ppsilv/vgaTerminal/Insumos/z80-002.jpeg

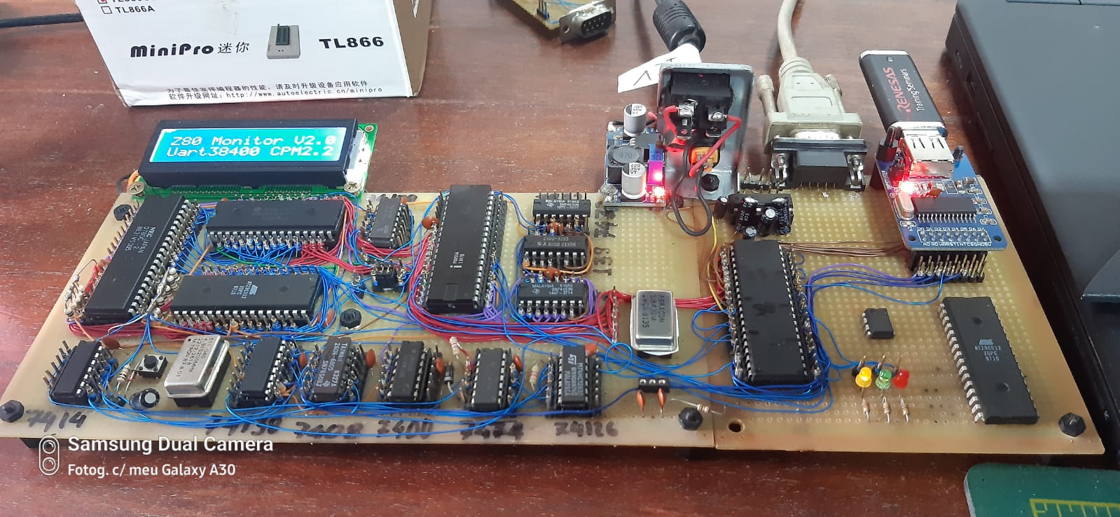
Insumos/z80-002.jpeg
