ppsilv/vgaTerminal/Insumos/z80-003.jpeg

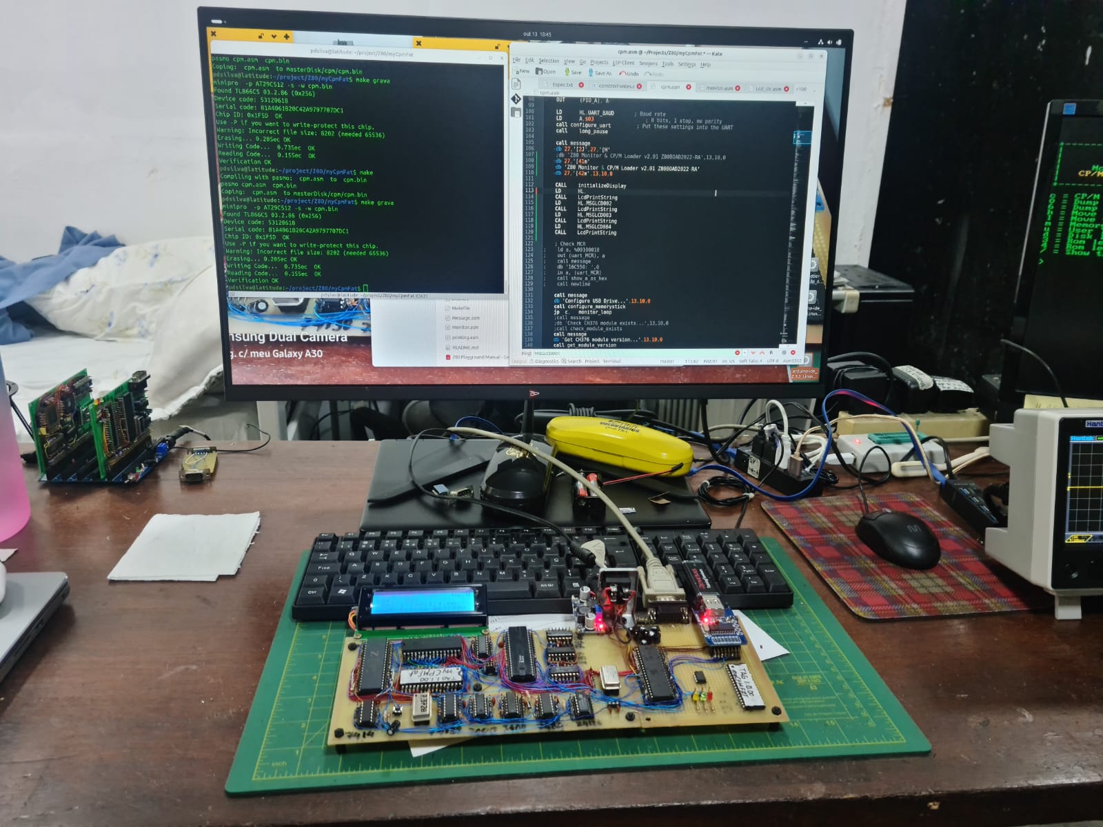
Insumos/z80-003.jpeg
