ppsilv/vgaTerminal/Docs/RS232_male2female.jpg

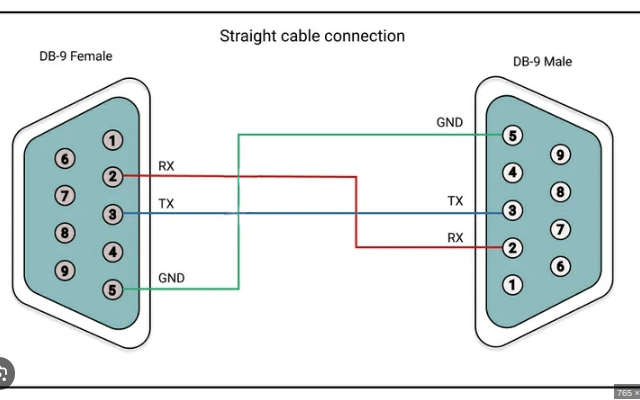
Docs/RS232_male2female.jpg
