ppsilv/vgaTerminal/Insumos/z80-001.jpeg

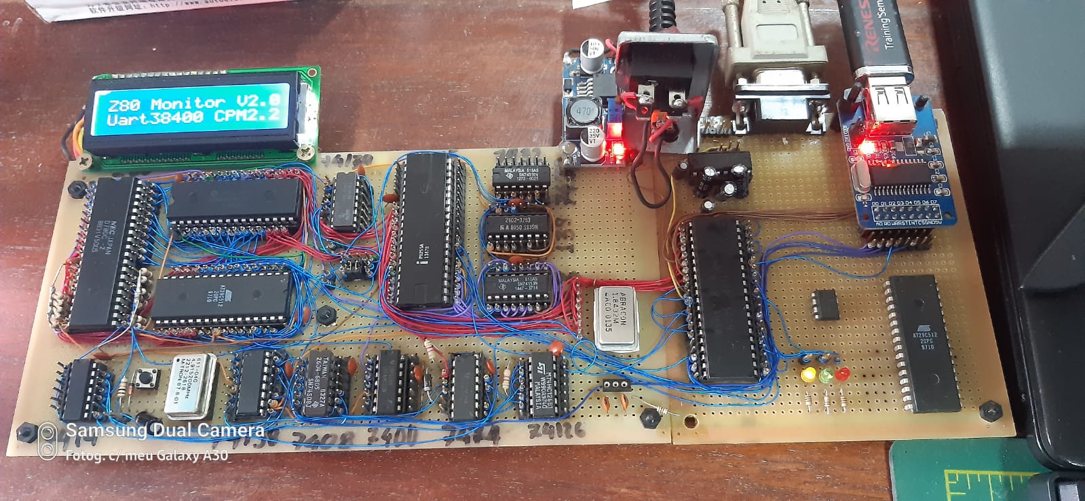
Insumos/z80-001.jpeg
