ppsilv/vgaTerminal/Insumos/z80-004.jpeg

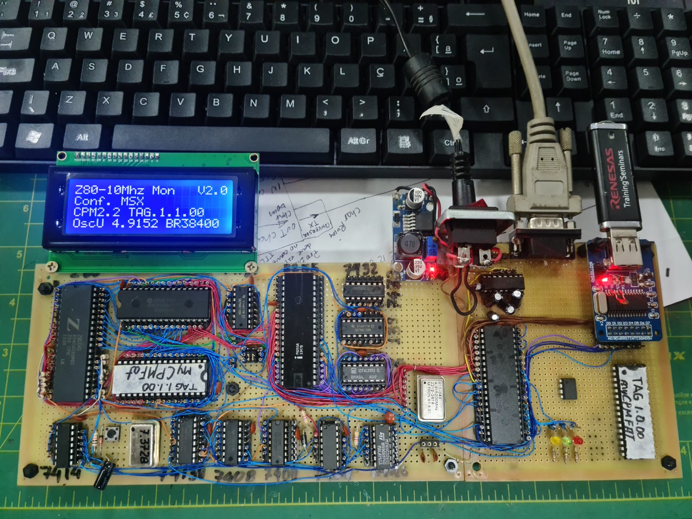
Insumos/z80-004.jpeg
