ppsilv/vgaTerminal/Insumos/z80-005.jpeg

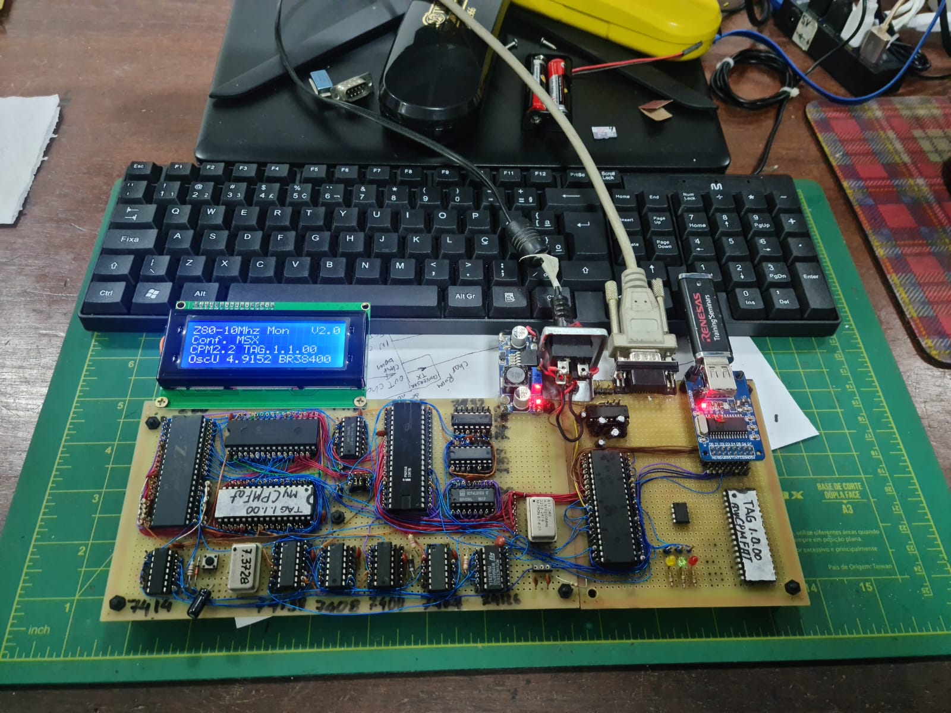
Insumos/z80-005.jpeg
