ppsilv/vgaTerminal/schematic/AnsiTerminal/AnsiTerminal.kicad_sch

## KiCad design schematic/AnsiTerminal/AnsiTerminal.kicad_sch (2024-10-10, an earlier design)

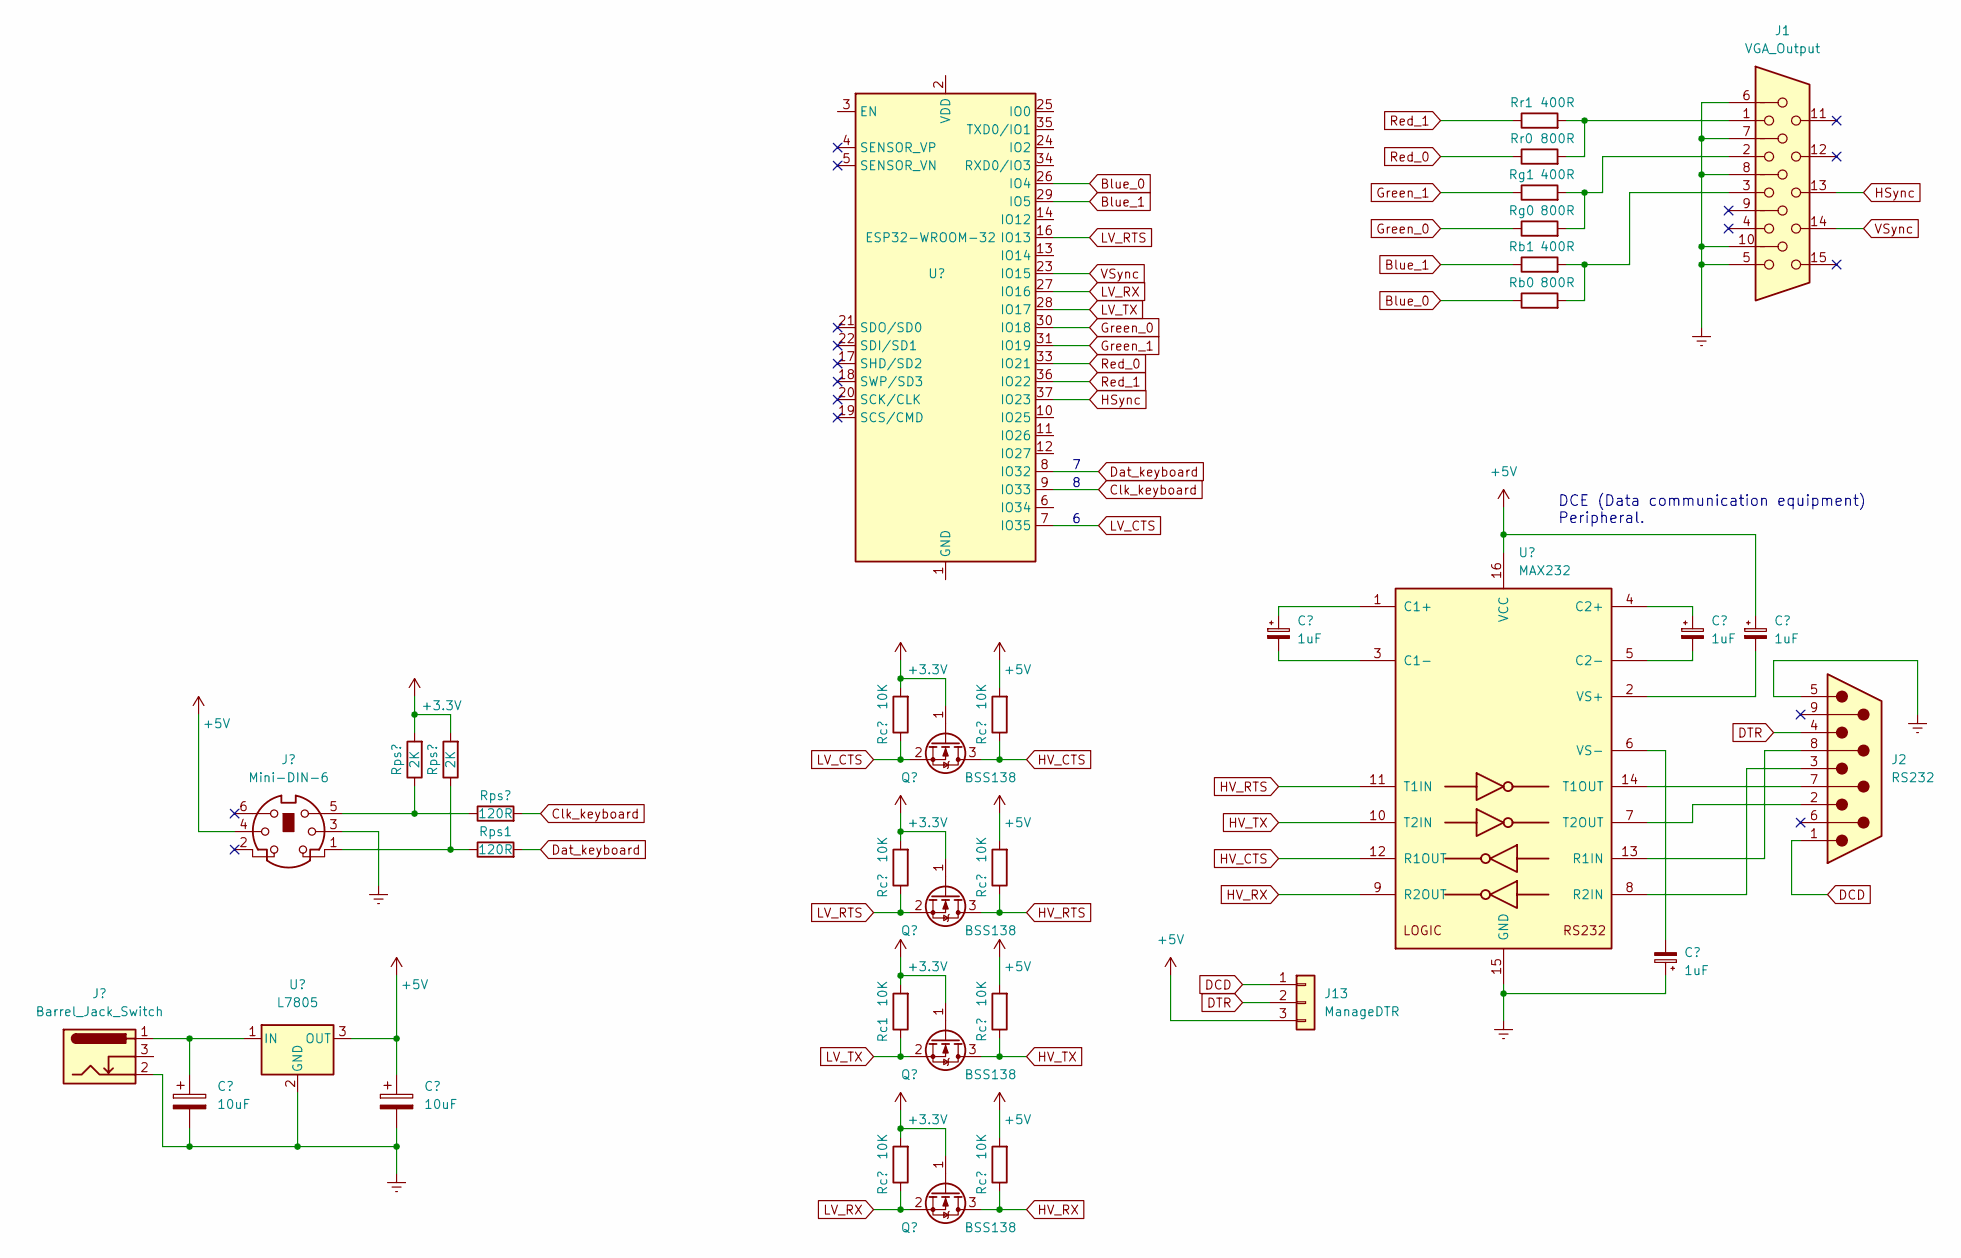
[picture p18: schematic AnsiTerminal.kicad_sch]

Parts:
J1: VGA_Output
J2: RS232
J13: ManageDTR
Rb0: 800R
Rb1: 400R
Rc1: 10K
Rg0: 800R
Rg1: 400R
Rps1: 120R
Rr0: 800R
Rr1: 400R

Connections:
Blue_0: Rb0.1
Blue_1: Rb1.1
DCD: J2.1, J13.1
DTR: J2.4, J13.2
Dat_keyboard: Rps1.2
Green_0: Rg0.1
Green_1: Rg1.1
HSync: J1.13
LV_TX: Rc1.1
unnamed: J1.1, Rr0.2, Rr1.2
unnamed: J1.2, Rg0.2, Rg1.2
unnamed: J1.3, Rb0.2, Rb1.2
unnamed: J1.5, J1.6, J1.7, J1.8, J1.10
Red_0: Rr0.1
Red_1: Rr1.1
VSync: J1.14

Notes on the sheet:
DCE (Data communication equipment) Peripheral.
