ppsilv/vgaTerminal/ESP32Lib/src/Graphics/Graphics.h

/*
	Author: bitluni 2019, refactoring by Martin-Laclaustra 2020
	License: 
	Creative Commons Attribution ShareAlike 4.0
	https://creativecommons.org/licenses/by-sa/4.0/
	
	For further details check out: 
		https://youtube.com/bitlunislab
		https://github.com/bitluni
		http://bitluni.net
*/

/*
Virtual function still needed in child classes
Color** allocateFrameBuffer()
Most virtual functions have been moved to templated static inheritance:

Inherited from InterfaceColor
typedef TYPE Color
colormask()
Color RGBA(int r, int g, int b, int a = 255) const
int R(Color c) const
int G(Color c) const
int B(Color c) const
int A(Color c) const

These functions are wrapped in virtual methods
void _dotFast(int x, int y, Color color)
Color _getFast(int x, int y)

They are composed of smaller components:

Inherited from BufferLayout
typedef TYPE BufferUnit
xpixperunit
ypixperunit
bufferdatamask
replicate (unused)
replicate32
swx
swy
shval
shbuf

Inherited from ColorToBuffer
coltobuf
buftocol
*/

#pragma once
#include <stdlib.h>
#include <math.h>
#include "Font.h"
#include "ImageDrawer.h"

#include "InterfaceColors.h"
#include "BufferLayouts.h"
#include "ColorToBuffer.h"

// Color defines the interface color, all interactions should use this
// BufferUnit defines how the color is actually stored in memory
template<class InterfaceColor, class BufferLayout, class ColorToBuffer>
class Graphics: public ImageDrawer, public InterfaceColor, public BufferLayout, public ColorToBuffer
{
  public:
	typedef typename InterfaceColor::Color Color;
	typedef typename BufferLayout::BufferUnit BufferGraphicsUnit;
	int cursorX, cursorY, cursorBaseX, cursorXIncrement, cursorYIncrement;
	Color frontColor, backColor;
	Font *font;
	int frameBufferCount;
	int currentFrameBuffer;
	BufferGraphicsUnit **frameBuffers[3];
	BufferGraphicsUnit **frontBuffer;
	BufferGraphicsUnit **backBuffer;
	bool autoScroll;
	//bool onScroll;
	size_t sizeOfBufferUnit = sizeof(BufferGraphicsUnit);
	int storageCoefficient = 1; //number of pixels in an BufferUnit variable
	int defaultBufferValue = 0;

	int xres;
	int yres;

	//pass templated functions
	static const int graphics_colormask()
	{
		return InterfaceColor::static_colormask();
	}
	static int graphics_swx(int x)
	{
		return BufferLayout::static_swx(x);
	}
	static int graphics_swy(int y)
	{
		return BufferLayout::static_swy(y);
	}
	static int graphics_shval(BufferGraphicsUnit val, int x, int y)
	{
		return BufferLayout::static_shval(val, x, y);
	}
	static int graphics_shbuf(BufferGraphicsUnit val, int x, int y)
	{
		return BufferLayout::static_shbuf(val, x, y);
	}
	static int graphics_coltobuf(int val, int x, int y)
	{
		return ColorToBuffer::coltobuf(val, x, y);
	}
	static int graphics_buftocol(int val)
	{
		return ColorToBuffer::buftocol(val);
	}

	void _dotFast(int x, int y, Color color)
	{
		//basic concept
		//backBuffer[y][x] = color;
		//decide x or y position[sw] -> shift depending (or not) on x or y[shval] -> mask[colormask] -> erase bits
		backBuffer[BufferLayout::static_swy(y)][BufferLayout::static_swx(x)] &= ~BufferLayout::static_shval(BufferLayout::static_bufferdatamask() & InterfaceColor::static_colormask(), x, y); // delete bits
		//mask[colormask] -> convert to buffer[coltobuf] -> shift depending (or not) on x or y[shval] -> decide x or y position[sw] -> store data
		backBuffer[BufferLayout::static_swy(y)][BufferLayout::static_swx(x)] |= BufferLayout::static_shval(ColorToBuffer::coltobuf(color & InterfaceColor::static_colormask(), x, y) & BufferLayout::static_bufferdatamask(), x, y); // write new bits
	}
	virtual void dotFast(int x, int y, Color color)
	{
		_dotFast(x, y, color);
	}
	virtual void dot(int x, int y, Color color)
	{
		if ((unsigned int)x < xres && (unsigned int)y < yres)
			_dotFast(x, y, color);
	}
	virtual void dotAdd(int x, int y, Color color)
	{
		Color oldColor = get(x, y);
		Color newColor = colorAdd(oldColor, color);
		dot(x, y, newColor);
	}
	virtual void dotMix(int x, int y, Color color)
	{
		Color oldColor = get(x, y);
		Color newColor = colorMix(oldColor, color);
		dot(x, y, newColor);
	}
	Color _getFast(int x, int y)
	{
		//basic concept
		//return backBuffer[y][x];
		//decide x or y position[sw] -> retrieve data -> shift depending (or not) on x or y[shbuf] -> mask[colormask] -> convert to color[buftocol]
		return ColorToBuffer::buftocol(BufferLayout::static_shbuf(backBuffer[BufferLayout::static_swy(y)][BufferLayout::static_swx(x)], x, y) & InterfaceColor::static_colormask());
	}
	virtual Color getFast(int x, int y)
	{
		return _getFast(x, y);
	}
	virtual Color get(int x, int y)
	{
		if ((unsigned int)x < xres && (unsigned int)y < yres)
			return _getFast(x, y);
		return 0;
	}
	//virtual BufferGraphicsUnit** allocateFrameBuffer() = 0;
	virtual BufferGraphicsUnit** allocateFrameBuffer()
	{
		//GraphicsCA8Swapped
		//return Graphics::allocateFrameBuffer(xres, yres, (BufferGraphicsUnit)levelBlack);
		//GraphicsR5G5B4S2Swapped
		//return Graphics::allocateFrameBuffer(xres, yres, (BufferGraphicsUnit)SBits);
		//GraphicsX8CA8Swapped
		//return Graphics::allocateFrameBuffer(xres, yres, (BufferGraphicsUnit)levelBlack<<8);
		//GraphicsX6S2W8RangedSwapped
		//return Graphics::allocateFrameBuffer(xres, yres, (BufferGraphicsUnit)(colorMinValue<<8)|SBits);
		//GraphicsW8RangedSwapped
		//return Graphics::allocateFrameBuffer(xres, yres, (BufferGraphicsUnit)colorMinValue);
		//GraphicsTextBuffer
		//return Graphics::allocateFrameBuffer(xres, yres, (BufferGraphicsUnit)32);
		//GraphicsW8
		//return Graphics::allocateFrameBuffer(xres, yres, (BufferGraphicsUnit)0);
		//GraphicsW1
		//return Graphics::allocateFrameBuffer(4*((xres + 3) / 4), (yres + static_ypixperunit() - 1) / static_ypixperunit(), (BufferGraphicsUnit)0);
		//GraphicsR5G5B4A2
		//return Graphics::allocateFrameBuffer(xres, yres, (BufferGraphicsUnit)0);
		//GraphicsR2G2B2S2Swapped
		//return Graphics::allocateFrameBuffer(xres, yres, (BufferGraphicsUnit)SBits);
		//GraphicsR2G2B2A2
		//return Graphics::allocateFrameBuffer(xres, yres, (BufferGraphicsUnit)0);
		//GraphicsR1G1B1X3S2Swapped
		//return Graphics::allocateFrameBuffer(xres, yres, (BufferGraphicsUnit)SBits);
		//GraphicsR1G1B1A1
		//return Graphics::allocateFrameBuffer((xres + static_xpixperunit() - 1) / static_xpixperunit(), yres, (BufferGraphicsUnit)0);
		return Graphics::allocateFrameBuffer(
			(xres + BufferLayout::static_xpixperunit() - 1) / BufferLayout::static_xpixperunit(),
			(yres + BufferLayout::static_ypixperunit() - 1) / BufferLayout::static_ypixperunit(),
			(BufferGraphicsUnit)defaultBufferValue);
		//TODO Fixes:
		// - round up x to multiples of 4 bytes (when necessary: in GraphicsW1 for renderer, in DMA buffers)
		//TODO:
		// - calculate and use byte-based allocation instead of unit/pixel based allocation
		//   (at this stage for some buffers the size of the buffer =/= xres, so in the next function "xres" is not such any more)
		// - move elsewhere: acondition the buffer with the fixed sync bytes or blank values
		//   this has to be done for all buffers allocated (front, back, and reserve)
	}
	virtual BufferGraphicsUnit** allocateFrameBuffer(int xres, int yres, BufferGraphicsUnit value)
	{
		BufferGraphicsUnit** frame = (BufferGraphicsUnit **)malloc(yres * sizeof(BufferGraphicsUnit *) );
		if(!frame)
			ERROR("Not enough memory for frame buffer");
		for (int y = 0; y < yres; y++)
		{
			frame[y] = (BufferGraphicsUnit *)malloc(xres * sizeof(BufferGraphicsUnit)+1000);
			if(!frame[y])
				ERROR("Not enough memory for frame buffer");
			for (int x = 0; x < xres; x++)
				frame[y][x] = value;
		}
		return frame;
	}
	static void **allocateRegularBufferArray(int count, int bytes)
	{
		void **arr = (void **)malloc(count * sizeof(void *));
		if(!arr)
			ERROR("Not enough regular memory");
		for (int i = 0; i < count; i++)
		{
			arr[i] = (void *)malloc(bytes);
			if(!arr[i])
				ERROR("Not enough regular memory");
		}
		return arr;
	}
	virtual Color colorAdd(Color colorOld, Color colorNew)
	{
		return InterfaceColor::static_colorAdd(colorOld, colorNew);
	}
	// Generic function currently not in use
	//virtual Color colorAdd(Color colorOld, Color colorNew)
	//{
		//int newR = R(colorOld)+R(colorNew);
		//newR = (newR > 255) ? 255 : newR;
		//int newG = G(colorOld)+G(colorNew);
		//newG = (newG > 255) ? 255 : newG;
		//int newB = B(colorOld)+B(colorNew);
		//newB = (newB > 255) ? 255 : newB;
		//int newA = A(colorOld)+A(colorNew);
		//newA = (newA > 255) ? 255 : newA;
		//return RGBA(newR, newG, newB, newA);
	//}
	virtual Color colorMix(Color colorOld, Color colorNew)
	{
		return InterfaceColor::static_colorMix(colorOld, colorNew);
	}
	// Generic function currently not in use
	//virtual Color colorMix(Color colorOld, Color colorNew)
	//{
		//int colorNewA = A(colorNew);
		//if (colorNewA != 0)
		//{
			//colorNewA = colorNewA + 1;
			//int newR = (R(colorOld)*(256-colorNewA)+R(colorNew)*colorNewA)>>8;
			//int newG = (G(colorOld)*(256-colorNewA)+G(colorNew)*colorNewA)>>8;
			//int newB = (B(colorOld)*(256-colorNewA)+B(colorNew)*colorNewA)>>8;
			//return RGBA(newR, newG, newB);
		//} else {
			//return colorOld;
		//}
	//}
	virtual Color RGBA(int r, int g, int b, int a = 255) const
	{
		return InterfaceColor::static_RGBA(r, g, b, a);
	}
	virtual int R(Color c) const
	{
		return InterfaceColor::static_R(c);
	}
	virtual int G(Color c) const
	{
		return InterfaceColor::static_G(c);
	}
	virtual int B(Color c) const
	{
		return InterfaceColor::static_B(c);
	}
	virtual int A(Color c) const
	{
		return InterfaceColor::static_A(c);
	}
	Color RGB(unsigned long rgb) const 
	{
		return RGBA(rgb & 255, (rgb >> 8) & 255, (rgb >> 16) & 255);
	}
	Color RGBA(unsigned long rgba) const 
	{
		return RGBA(rgba & 255, (rgba >> 8) & 255, (rgba >> 16) & 255, rgba >> 24);
	}
	Color RGB(int r, int g, int b) const 
	{
		return RGBA(r, g, b);
	}

	void setFrameBufferCount(unsigned char i)
	{
		frameBufferCount = i > 3 ? 3 : i;
	}

	virtual void show(bool vSync = false)
	{
		if(!frameBufferCount)
			return;
		currentFrameBuffer = (currentFrameBuffer + 1) % frameBufferCount;
		frontBuffer = frameBuffers[currentFrameBuffer];
		backBuffer = frameBuffers[(currentFrameBuffer + frameBufferCount - 1) % frameBufferCount];
		Serial.print("yres * sizeof(BufferGraphicsUnit *).:");
		Serial.println(yres * sizeof(BufferGraphicsUnit *));
		//Serial.print("frameBufferCount...:");Serial.println(frameBufferCount);
		//Serial.print("backBuffer.........:");Serial.println(backBuffer);
	}

	Graphics(int xres = 0, int yres = 0)
	{
		this->xres = xres;
		this->yres = yres;
		font = 0;
		cursorX = cursorY = cursorBaseX = 0;
		cursorXIncrement = cursorYIncrement = 1;
		frontColor = -1;
		backColor = 0;
		frameBufferCount = 1;
		for(int i = 0; i < 3; i++)
			frameBuffers[i] = 0;
		frontBuffer = 0;
		backBuffer = 0;
		autoScroll = true;
	}

	virtual bool allocateFrameBuffers()
	{
		if(yres <= 0 || xres <= 0)
			return false;
		for(int i = 0; i < frameBufferCount; i++)
			frameBuffers[i] = allocateFrameBuffer();
		currentFrameBuffer = 0;
		show();
		return true;
	}

	virtual void setResolution(int xres, int yres)
	{
		this->xres = xres;
		this->yres = yres;
		allocateFrameBuffers();
	}

	virtual float pixelAspect() const
	{
		return 1;
	}

	void setTextColor(long front, long back = 0)
	{
		frontColor = front;
		backColor = back;
	}

	virtual void setFont(Font &font)
	{
		this->font = &font;
		cursorXIncrement = this->font->charWidth;
		cursorYIncrement = this->font->charHeight;
	}

	void setCursor(int x, int y)
	{
		cursorX = cursorBaseX = x;
		cursorY = y;
	}

	void setCursorText(int x, int y)
	{
		cursorX = cursorBaseX = x * font->charWidth;
		cursorY = y * font->charHeight;
	}


	virtual void drawChar(int x, int y, int ch)
	{
		if (!font)
			return;
		if (!font->valid(ch))
			return;
		const unsigned char *pix = &font->pixels[font->charWidth * font->charHeight * (ch - font->firstChar)];
		for (int py = 0; py < font->charHeight; py++)
			for (int px = 0; px < font->charWidth; px++)
				if (*(pix++))
					dotMix(px + x, py + y, frontColor);
				else
					dotMix(px + x, py + y, backColor);
	}

	virtual void drawChar(int ch,bool clear)
	{
		if( clear ){
			for (int py = 0; py < font->charHeight; py++)
				for (int px = 0; px < font->charWidth; px++)
					dot(px + cursorX, py + cursorY, backColor);
		}else{
			const unsigned char *pix = &font->pixels[font->charWidth * font->charHeight * (ch - font->firstChar)];
			for (int py = 0; py < font->charHeight; py++)
				for (int px = 0; px < font->charWidth; px++)
					if (*(pix++))
						dot(px + cursorX, py + cursorY, frontColor);
					else
						dot(px + cursorX, py + cursorY, backColor);
		}
	}
	void printCursor(void)
	{
		drawChar('_',false);
	}

	void clearCursor(void)
	{
		drawChar('_',true);
	}

	void setCursorBS()
	{
		//Serial.println(cursorX);
		if (cursorX == 0){
			cursorY -= this->font->charHeight;
			cursorX = 79*this->font->charWidth;
		}else{
			cursorX -= this->font->charWidth;
		}
		//cursorY += y;
	}

	void print(const char ch)
	{
		if (!font)
			return;

		if(ch == '\n')
		{
			cursorX = 0;//cursorBaseX;
			cursorY += cursorYIncrement;
		}
		else if (font->valid(ch)){
			drawChar(cursorX, cursorY, ch);
			cursorX += cursorXIncrement;
		}
		else{
			drawChar(cursorX, cursorY, ' ');
		}

		if ( (cursorX + cursorXIncrement) > xres )
		{
			cursorY += cursorYIncrement;
			cursorX = cursorBaseX;
			if( cursorY > yres ){
				cursorY = yres-cursorYIncrement;
			}
		}
		if ( (cursorY + cursorYIncrement) > yres  )
		{
			if(autoScroll && ( (cursorY + cursorYIncrement) > yres) ){
				//onScroll = true;
				//Serial.print("\nCursorY ");Serial.print(cursorY);
				//Serial.print(" yres ");Serial.print(yres);
				//Serial.print(" cursorYIncrement ");Serial.print(cursorYIncrement);
				scroll((cursorY - yres)+cursorYIncrement, backColor);
			}
		}
	}
	//bool getOnScroll(){
	//	return onScroll;
	//}
	void println(const char ch)
	{
		print(ch);
		print("\n");
	}

	void print(const char *str)
	{
		if (!font)
			return;
		while (*str)
		{
			print(*str);
			str++;
		}
	}

	void println(const char *str)
	{
		print(str);
		print("\n");
	}

	void print(long number, int base = 10, int minCharacters = 1)
	{
		if(minCharacters < 1)
			minCharacters = 1;
		bool sign = number < 0;
		if (sign)
			number = -number;
		const char baseChars[] = "0123456789ABCDEF";
		char temp[33];
		temp[32] = 0;
		int i = 31;
		do
		{
			temp[i--] = baseChars[number % base];
			number /= base;
		} while (number > 0);
		if (sign)
			temp[i--] = '-';
		for (; i > 31 - minCharacters; i--)
			temp[i] = ' ';
		print(&temp[i + 1]);
	}

	void print(unsigned long number, int base = 10, int minCharacters = 1)
	{
		if(minCharacters < 1)
			minCharacters = 1;
		const char baseChars[] = "0123456789ABCDEF";
		char temp[33];
		temp[32] = 0;
		int i = 31;
		do
		{
			temp[i--] = baseChars[number % base];
			number /= base;
		} while (number > 0);
		for (; i > 31 - minCharacters; i--)
			temp[i] = ' ';
		print(&temp[i + 1]);
	}	

	void println(long number, int base = 10, int minCharacters = 1)
	{
		print(number, base, minCharacters); print("\n");
	}

	void println(unsigned long number, int base = 10, int minCharacters = 1)
	{
		print(number, base, minCharacters); print("\n");
	}

	void print(int number, int base = 10, int minCharacters = 1)
	{
		print(long(number), base, minCharacters);
	}

	void println(int number, int base = 10, int minCharacters = 1)
	{
		println(long(number), base, minCharacters);
	}

	void print(unsigned int number, int base = 10, int minCharacters = 1)
	{
		print((unsigned long)(number), base, minCharacters);
	}

	void println(unsigned int number, int base = 10, int minCharacters = 1)
	{
		println((unsigned long)(number), base, minCharacters);
	}

	void print(short number, int base = 10, int minCharacters = 1)
	{
		print(long(number), base, minCharacters);
	}

	void println(short number, int base = 10, int minCharacters = 1)
	{
		println(long(number), base, minCharacters);
	}

	void print(unsigned short number, int base = 10, int minCharacters = 1)
	{
		print(long(number), base, minCharacters);
	}

	void println(unsigned short number, int base = 10, int minCharacters = 1)
	{
		println(long(number), base, minCharacters);
	}

	void print(unsigned char number, int base = 10, int minCharacters = 1)
	{
		print(long(number), base, minCharacters);
	}

	void println(unsigned char number, int base = 10, int minCharacters = 1)
	{
		println(long(number), base, minCharacters);
	}

	void println()
	{
		print("\n");
	}

	void print(double number, int fractionalDigits = 2, int minCharacters = 1)
	{
		long p = long(pow(10, fractionalDigits));
		long long n = (double(number) * p + 0.5f);
		print(long(n / p), 10, minCharacters - 1 - fractionalDigits);
		if(fractionalDigits)
		{
			print(".");
			for(int i = 0; i < fractionalDigits; i++)
			{
				p /= 10;
				print(long(n / p) % 10);
			}
		}
	}

	void println(double number, int fractionalDigits = 2, int minCharacters = 1)
	{
		print(number, fractionalDigits, minCharacters); 
		print("\n");
	}

	virtual void clear(Color color = 0)
	{
		for (int y = 0; y < yres; y++)
			for (int x = 0; x < xres; x++)
				dotFast(x, y, color);
	}

	virtual void xLine(int x0, int x1, int y, Color color)
	{
		if (y < 0 || y >= yres)
			return;
		if (x0 > x1)
		{
			int xb = x0;
			x0 = x1;
			x1 = xb;
		}
		if (x0 < 0)
			x0 = 0;
		if (x1 > xres)
			x1 = xres;
		for (int x = x0; x < x1; x++)
			dotFast(x, y, color);
	}

	void triangle(short *v0, short *v1, short *v2, Color color)
	{
		short *v[3] = {v0, v1, v2};
		if (v[1][1] < v[0][1])
		{
			short *vb = v[0];
			v[0] = v[1];
			v[1] = vb;
		}
		if (v[2][1] < v[1][1])
		{
			short *vb = v[1];
			v[1] = v[2];
			v[2] = vb;
		}
		if (v[1][1] < v[0][1])
		{
			short *vb = v[0];
			v[0] = v[1];
			v[1] = vb;
		}
		int y = v[0][1];
		int xac = v[0][0] << 16;
		int xab = v[0][0] << 16;
		int xbc = v[1][0] << 16;
		int xaci = 0;
		int xabi = 0;
		int xbci = 0;
		if (v[1][1] != v[0][1])
			xabi = ((v[1][0] - v[0][0]) << 16) / (v[1][1] - v[0][1]);
		if (v[2][1] != v[0][1])
			xaci = ((v[2][0] - v[0][0]) << 16) / (v[2][1] - v[0][1]);
		if (v[2][1] != v[1][1])
			xbci = ((v[2][0] - v[1][0]) << 16) / (v[2][1] - v[1][1]);

		for (; y < v[1][1] && y < yres; y++)
		{
			if (y >= 0)
				xLine(xab >> 16, xac >> 16, y, color);
			xab += xabi;
			xac += xaci;
		}
		for (; y < v[2][1] && y < yres; y++)
		{
			if (y >= 0)
				xLine(xbc >> 16, xac >> 16, y, color);
			xbc += xbci;
			xac += xaci;
		}
	}

	void line(int x1, int y1, int x2, int y2, Color color)
	{
		int x, y, xe, ye;
		int dx = x2 - x1;
		int dy = y2 - y1;
		int dx1 = labs(dx);
		int dy1 = labs(dy);
		int px = 2 * dy1 - dx1;
		int py = 2 * dx1 - dy1;
		if (dy1 <= dx1)
		{
			if (dx >= 0)
			{
				x = x1;
				y = y1;
				xe = x2;
			}
			else
			{
				x = x2;
				y = y2;
				xe = x1;
			}
			dot(x, y, color);
			for (int i = 0; x < xe; i++)
			{
				x = x + 1;
				if (px < 0)
				{
					px = px + 2 * dy1;
				}
				else
				{
					if ((dx < 0 && dy < 0) || (dx > 0 && dy > 0))
					{
						y = y + 1;
					}
					else
					{
						y = y - 1;
					}
					px = px + 2 * (dy1 - dx1);
				}
				dot(x, y, color);
			}
		}
		else
		{
			if (dy >= 0)
			{
				x = x1;
				y = y1;
				ye = y2;
			}
			else
			{
				x = x2;
				y = y2;
				ye = y1;
			}
			dot(x, y, color);
			for (int i = 0; y < ye; i++)
			{
				y = y + 1;
				if (py <= 0)
				{
					py = py + 2 * dx1;
				}
				else
				{
					if ((dx < 0 && dy < 0) || (dx > 0 && dy > 0))
					{
						x = x + 1;
					}
					else
					{
						x = x - 1;
					}
					py = py + 2 * (dx1 - dy1);
				}
				dot(x, y, color);
			}
		}
	}

	void fillRect(int x, int y, int w, int h, Color color)
	{
		if (x < 0)
		{
			w += x;
			x = 0;
		}
		if (y < 0)
		{
			h += y;
			y = 0;
		}
		if (x + w > xres)
			w = xres - x;
		if (y + h > yres)
			h = yres - y;
		for (int j = y; j < y + h; j++)
			for (int i = x; i < x + w; i++)
				dotFast(i, j, color);
	}

	void rect(int x, int y, int w, int h, Color color)
	{
		fillRect(x, y, w, 1, color);
		fillRect(x, y, 1, h, color);
		fillRect(x, y + h - 1, w, 1, color);
		fillRect(x + w - 1, y, 1, h, color);
	}

	void circle(int x, int y, int r, Color color)
	{
		int oxr = r;
		for(int i = 0; i < r + 1; i++)
		{
			int xr = (int)sqrt(r * r - i * i);
			xLine(x - oxr, x - xr + 1, y + i, color);
			xLine(x + xr, x + oxr + 1, y + i, color);
			if(i) 
			{
				xLine(x - oxr, x - xr + 1, y - i, color);
				xLine(x + xr, x + oxr + 1, y - i, color);
			}
			oxr = xr;
		}
	}

	void fillCircle(int x, int y, int r, Color color)
	{
		for(int i = 0; i < r + 1; i++)
		{
			int xr = (int)sqrt(r * r - i * i);
			xLine(x - xr, x + xr + 1, y + i, color);
			if(i) 
				xLine(x - xr, x + xr + 1, y - i, color);
		}
	}

	void ellipse(int x, int y, int rx, int ry, Color color)
	{
		if(ry == 0)
			return;
		int oxr = rx;
		float f = float(rx) / ry;
		f *= f;
		for(int i = 0; i < ry + 1; i++)
		{
			float s = rx * rx - i * i * f;
			int xr = (int)sqrt(s <= 0 ? 0 : s);
			xLine(x - oxr, x - xr + 1, y + i, color);
			xLine(x + xr, x + oxr + 1, y + i, color);
			if(i) 
			{
				xLine(x - oxr, x - xr + 1, y - i, color);
				xLine(x + xr, x + oxr + 1, y - i, color);
			}
			oxr = xr;
		}
	}

	void fillEllipse(int x, int y, int rx, int ry, Color color)
	{
		if(ry == 0)
			return;
		float f = float(rx) / ry;
		f *= f;		
		for(int i = 0; i < ry + 1; i++)
		{
			float s = rx * rx - i * i * f;
			int xr = (int)sqrt(s <= 0 ? 0 : s);
			xLine(x - xr, x + xr + 1, y + i, color);
			if(i) 
				xLine(x - xr, x + xr + 1, y - i, color);
		}
	}

	virtual void scroll(int dy, Color color)
	{
		//static int dyA;
		//dyA = dy;
		//lixo 1 some primeiro char
		//if( dy == 2 && dyA != 2 )
		//	dy = 8;
		//else if( dy == 4 )
		//	dy = 8;
		//else if( dy > 0 )
		//	dy = 9 - dy;
		//cursorY -= font->charHeight;

		if(dy > 0)
		{
			for(int d = 0; d < dy; d++)
			{
				BufferGraphicsUnit *l = backBuffer[0];
				for(int i = 0; i < yres - 1; i++)
				{
					backBuffer[i] = backBuffer[i + 1];
				}
				backBuffer[yres - 1] = l;
				//xLine(0, xres-font->charWidth, yres - 1, color);
				xLine(0, xres , yres - 1, color);
			}
		}
		//else
		//{
		//	for(int d = 0; d < -dy; d++)
		//	{
		//		BufferGraphicsUnit *l = backBuffer[yres - 1];
		//		for(int i = yres - 1; i > 0; i--)
		//		{
		//			backBuffer[i] = backBuffer[i - 1];
		//		}
		//		backBuffer[0] = l;
		//		xLine(0, xres, 0, color);
		//	}
		//}
		//cursorY -= font->charHeight;
		cursorY -= dy;
	}

	virtual Color R5G5B4A2ToColor(unsigned short c)
	{
		int r = (((c << 1) & 0x3e) * 255 + 1) / 0x3e;
		int g = (((c >> 4) & 0x3e) * 255 + 1) / 0x3e;
		int b = (((c >> 9) & 0x1e) * 255 + 1) / 0x1e;
		int a = (((c >> 13) & 6) * 255 + 1) / 6;
		return RGBA(r, g, b, a);
	}

	virtual Color R2G2B2A2ToColor(unsigned char c)
	{
		int r = ((int(c) & 3) * 255 + 1) / 3;
		int g = (((int(c) >> 2) & 3) * 255 + 1) / 3;
		int b = (((int(c) >> 4) & 3) * 255 + 1) / 3;
		int a = (((int(c) >> 6) & 3) * 255 + 1) / 3;
		return RGBA(r, g, b, a);
	}

	virtual Color R4G4B4A4ToColor(unsigned short c)
	{
		int r = (((c << 1) & 0x1e) * 255 + 1) / 0x1e;
		int g = (((c >> 3) & 0x1e) * 255 + 1) / 0x1e;
		int b = (((c >> 7) & 0x1e) * 255 + 1) / 0x1e;
		int a = (((c >> 11) & 0x1e) * 255 + 1) / 0x1e;
		return RGBA(r, g, b, a);
	}

	virtual Color R8G8B8A8ToColor(unsigned long c)
	{
		return RGBA(c & 255, (c >> 8) & 255, (c >> 16) & 255, (c >> 24) & 255);
	}

	virtual void imageR8G8B8A8(Image &image, int x, int y, int srcX, int srcY, int srcXres, int srcYres)
	{
		for (int py = 0; py < srcYres; py++)
		{
			int i = srcX + (py + srcY) * image.xres;
			for (int px = 0; px < srcXres; px++)
				dot(px + x, py + y, R8G8B8A8ToColor(((unsigned long*)image.pixels)[i++]));
		}		
	}

	virtual void imageAddR8G8B8A8(Image &image, int x, int y, int srcX, int srcY, int srcXres, int srcYres)
	{
		for (int py = 0; py < srcYres; py++)
		{
			int i = srcX + (py + srcY) * image.xres;
			for (int px = 0; px < srcXres; px++)
				dotAdd(px + x, py + y, R8G8B8A8ToColor(((unsigned long*)image.pixels)[i++]));
		}
	}

	virtual void imageMixR8G8B8A8(Image &image, int x, int y, int srcX, int srcY, int srcXres, int srcYres)
	{
		for (int py = 0; py < srcYres; py++)
		{
			int i = srcX + (py + srcY) * image.xres;
			for (int px = 0; px < srcXres; px++)
				dotMix(px + x, py + y, R8G8B8A8ToColor(((unsigned long*)image.pixels)[i++]));
		}
	}	

	virtual void imageR4G4B4A4(Image &image, int x, int y, int srcX, int srcY, int srcXres, int srcYres)
	{
		for (int py = 0; py < srcYres; py++)
		{
			int i = srcX + (py + srcY) * image.xres;
			for (int px = 0; px < srcXres; px++)
				dot(px + x, py + y, R4G4B4A4ToColor(((unsigned short*)image.pixels)[i++]));
		}		
	}

	virtual void imageAddR4G4B4A4(Image &image, int x, int y, int srcX, int srcY, int srcXres, int srcYres)
	{
		for (int py = 0; py < srcYres; py++)
		{
			int i = srcX + (py + srcY) * image.xres;
			for (int px = 0; px < srcXres; px++)
				dotAdd(px + x, py + y, R4G4B4A4ToColor(((unsigned short*)image.pixels)[i++]));
		}
	}

	virtual void imageMixR4G4B4A4(Image &image, int x, int y, int srcX, int srcY, int srcXres, int srcYres)
	{
		for (int py = 0; py < srcYres; py++)
		{
			int i = srcX + (py + srcY) * image.xres;
			for (int px = 0; px < srcXres; px++)
				dotMix(px + x, py + y, R4G4B4A4ToColor(((unsigned short*)image.pixels)[i++]));
		}
	}	

	virtual void imageR5G5B4A2(Image &image, int x, int y, int srcX, int srcY, int srcXres, int srcYres)
	{
		for (int py = 0; py < srcYres; py++)
		{
			int i = srcX + (py + srcY) * image.xres;
			for (int px = 0; px < srcXres; px++)
				dot(px + x, py + y, R5G5B4A2ToColor(((unsigned short*)image.pixels)[i++]));
		}		
	}

	virtual void imageAddR5G5B4A2(Image &image, int x, int y, int srcX, int srcY, int srcXres, int srcYres)
	{
		for (int py = 0; py < srcYres; py++)
		{
			int i = srcX + (py + srcY) * image.xres;
			for (int px = 0; px < srcXres; px++)
				dotAdd(px + x, py + y, R5G5B4A2ToColor(((unsigned short*)image.pixels)[i++]));
		}
	}

	virtual void imageMixR5G5B4A2(Image &image, int x, int y, int srcX, int srcY, int srcXres, int srcYres)
	{
		for (int py = 0; py < srcYres; py++)
		{
			int i = srcX + (py + srcY) * image.xres;
			for (int px = 0; px < srcXres; px++)
				dotMix(px + x, py + y, R5G5B4A2ToColor(((unsigned short*)image.pixels)[i++]));
		}
	}	

	virtual void imageR2G2B2A2(Image &image, int x, int y, int srcX, int srcY, int srcXres, int srcYres)
	{
		for (int py = 0; py < srcYres; py++)
		{
			int i = srcX + (py + srcY) * image.xres;
			for (int px = 0; px < srcXres; px++)
				dot(px + x, py + y, R2G2B2A2ToColor(((unsigned char*)image.pixels)[i++]));
		}		
	}

	virtual void imageAddR2G2B2A2(Image &image, int x, int y, int srcX, int srcY, int srcXres, int srcYres)
	{
		for (int py = 0; py < srcYres; py++)
		{
			int i = srcX + (py + srcY) * image.xres;
			for (int px = 0; px < srcXres; px++)
				dotAdd(px + x, py + y, R2G2B2A2ToColor(((unsigned char*)image.pixels)[i++]));
		}
	}

	virtual void imageMixR2G2B2A2(Image &image, int x, int y, int srcX, int srcY, int srcXres, int srcYres)
	{
		for (int py = 0; py < srcYres; py++)
		{
			int i = srcX + (py + srcY) * image.xres;
			for (int px = 0; px < srcXres; px++)
				dotMix(px + x, py + y, R2G2B2A2ToColor(((unsigned char*)image.pixels)[i++]));
		}
	}	
};
