ppsilv/vgaTerminal/KeybLayout.h

#ifndef __KEYBLAYOUT_H__
#define __KEYBLAYOUT_H__


const PS2Keymap_t PS2Keymap_US = {
  // without shift
	{0, PS2_F9, 0, PS2_F5, PS2_F3, PS2_F1, PS2_F2, PS2_F12,
	0, PS2_F10, PS2_F8, PS2_F6, PS2_F4, PS2_TAB, '`', 0,
	0, 0 /*Lalt*/, 0 /*Lshift*/, 0, 0 /*Lctrl*/, 'q', '1', 0,
	0, 0, 'z', 's', 'a', 'w', '2', 0,
	0, 'c', 'x', 'd', 'e', '4', '3', 0,
	0, ' ', 'v', 'f', 't', 'r', '5', 0,
	0, 'n', 'b', 'h', 'g', 'y', '6', 0,
	0, 0, 'm', 'j', 'u', '7', '8', 0,
	0, ',', 'k', 'i', 'o', '0', '9', 0,
	0, '.', '/', 'l', ';', 'p', '-', 0,
	0, 0, '\'', 0, '[', '=', 0, 0,
	0 /*CapsLock*/, 0 /*Rshift*/, PS2_ENTER /*Enter*/, ']', 0, '\\', 0, 0,
	0, 0, 0, 0, 0, 0, PS2_BACKSPACE, 0,
	0, '1', 0, '4', '7', 0, 0, 0,
	'0', '.', '2', '5', '6', '8', PS2_ESC, 0 /*NumLock*/,
	PS2_F11, '+', '3', '-', '*', '9', PS2_SCROLL, 0,
	0, 0, 0, PS2_F7 },
  // with shift
	{0, PS2_F9, 0, PS2_F5, PS2_F3, PS2_F1, PS2_F2, PS2_F12,
	0, PS2_F10, PS2_F8, PS2_F6, PS2_F4, PS2_TAB, '~', 0,
	0, 0 /*Lalt*/, 0 /*Lshift*/, 0, 0 /*Lctrl*/, 'Q', '!', 0,
	0, 0, 'Z', 'S', 'A', 'W', '@', 0,
	0, 'C', 'X', 'D', 'E', '$', '#', 0,
	0, ' ', 'V', 'F', 'T', 'R', '%', 0,
	0, 'N', 'B', 'H', 'G', 'Y', '^', 0,
	0, 0, 'M', 'J', 'U', '&', '*', 0,
	0, '<', 'K', 'I', 'O', ')', '(', 0,
	0, '>', '?', 'L', ':', 'P', '_', 0,
	0, 0, '"', 0, '{', '+', 0, 0,
	0 /*CapsLock*/, 0 /*Rshift*/, PS2_ENTER /*Enter*/, '}', 0, '|', 0, 0,
	0, 0, 0, 0, 0, 0, PS2_BACKSPACE, 0,
	0, '1', 0, '4', '7', 0, 0, 0,
	'0', '.', '2', '5', '6', '8', PS2_ESC, 0 /*NumLock*/,
	PS2_F11, '+', '3', '-', '*', '9', PS2_SCROLL, 0,
	0, 0, 0, PS2_F7 },
  // with caps and shift 
	{0, PS2_F9, 0, PS2_F5, PS2_F3, PS2_F1, PS2_F2, PS2_F12,
	0, PS2_F10, PS2_F8, PS2_F6, PS2_F4, PS2_TAB, '~', 0,
	0, 0 /*Lalt*/, 0 /*Lshift*/, 0, 0 /*Lctrl*/, 'q', '!', 0,
	0, 0, 'z', 's', 'a', 'w', '@', 0,
	0, 'c', 'x', 'd', 'e', '$', '#', 0,
	0, ' ', 'v', 'f', 't', 'r', '%', 0,
	0, 'n', 'b', 'h', 'g', 'y', '^', 0,
	0, 0, 'm', 'j', 'u', '&', '*', 0,
	0, '<', 'k', 'i', 'o', ')', '(', 0,
	0, '>', '?', 'l', ':', 'p', '_', 0,
	0, 0, '"', 0, '{', '+', 0, 0,
	0 /*CapsLock*/, 0 /*Rshift*/, PS2_ENTER /*Enter*/, '}', 0, '|', 0, 0,
	0, 0, 0, 0, 0, 0, PS2_BACKSPACE, 0,
	0, '1', 0, '4', '7', 0, 0, 0,
	'0', '.', '2', '5', '6', '8', PS2_ESC, 0 /*NumLock*/,
	PS2_F11, '+', '3', '-', '*', '9', PS2_SCROLL, 0,
	0, 0, 0, PS2_F7 }, 
	0,
};

#ifdef TODOS_PAISES
const PS2Keymap_t PS2Keymap_German = {
  // without shift
	{0, PS2_F9, 0, PS2_F5, PS2_F3, PS2_F1, PS2_F2, PS2_F12,
	0, PS2_F10, PS2_F8, PS2_F6, PS2_F4, PS2_TAB, '^', 0,
	0, 0 /*Lalt*/, 0 /*Lshift*/, 0, 0 /*Lctrl*/, 'q', '1', 0,
	0, 0, 'y', 's', 'a', 'w', '2', 0,
	0, 'c', 'x', 'd', 'e', '4', '3', 0,
	0, ' ', 'v', 'f', 't', 'r', '5', 0,
	0, 'n', 'b', 'h', 'g', 'z', '6', 0,
	0, 0, 'm', 'j', 'u', '7', '8', 0,
	0, ',', 'k', 'i', 'o', '0', '9', 0,
	0, '.', '-', 'l', PS2_o_DIAERESIS, 'p', PS2_SHARP_S, 0,
	0, 0, PS2_a_DIAERESIS, 0, PS2_u_DIAERESIS, '\'', 0, 0,
	0 /*CapsLock*/, 0 /*Rshift*/, PS2_ENTER /*Enter*/, '+', 0, '#', 0, 0,
	0, '<', 0, 0, 0, 0, PS2_BACKSPACE, 0,
	0, '1', 0, '4', '7', 0, 0, 0,
	'0', '.', '2', '5', '6', '8', PS2_ESC, 0 /*NumLock*/,
	PS2_F11, '+', '3', '-', '*', '9', PS2_SCROLL, 0,
	0, 0, 0, PS2_F7 },
  // with shift
	{0, PS2_F9, 0, PS2_F5, PS2_F3, PS2_F1, PS2_F2, PS2_F12,
	0, PS2_F10, PS2_F8, PS2_F6, PS2_F4, PS2_TAB, PS2_DEGREE_SIGN, 0,
	0, 0 /*Lalt*/, 0 /*Lshift*/, 0, 0 /*Lctrl*/, 'Q', '!', 0,
	0, 0, 'Y', 'S', 'A', 'W', '"', 0,
	0, 'C', 'X', 'D', 'E', '$', PS2_SECTION_SIGN, 0,
	0, ' ', 'V', 'F', 'T', 'R', '%', 0,
	0, 'N', 'B', 'H', 'G', 'Z', '&', 0,
	0, 0, 'M', 'J', 'U', '/', '(', 0,
	0, ';', 'K', 'I', 'O', '=', ')', 0,
	0, ':', '_', 'L', PS2_O_DIAERESIS, 'P', '?', 0,
	0, 0, PS2_A_DIAERESIS, 0, PS2_U_DIAERESIS, '`', 0, 0,
	0 /*CapsLock*/, 0 /*Rshift*/, PS2_ENTER /*Enter*/, '*', 0, '\'', 0, 0,
	0, '>', 0, 0, 0, 0, PS2_BACKSPACE, 0,
	0, '1', 0, '4', '7', 0, 0, 0,
	'0', '.', '2', '5', '6', '8', PS2_ESC, 0 /*NumLock*/,
	PS2_F11, '+', '3', '-', '*', '9', PS2_SCROLL, 0,
	0, 0, 0, PS2_F7 },
	1,
  // with altgr
	{0, PS2_F9, 0, PS2_F5, PS2_F3, PS2_F1, PS2_F2, PS2_F12,
	0, PS2_F10, PS2_F8, PS2_F6, PS2_F4, PS2_TAB, 0, 0,
	0, 0 /*Lalt*/, 0 /*Lshift*/, 0, 0 /*Lctrl*/, '@', 0, 0,
	0, 0, 0, 0, 0, 0, PS2_SUPERSCRIPT_TWO, 0,
	0, 0, 0, 0, PS2_CURRENCY_SIGN, 0, PS2_SUPERSCRIPT_THREE, 0,
	0, 0, 0, 0, 0, 0, 0, 0,
	0, 0, 0, 0, 0, 0, 0, 0,
	0, 0, PS2_MICRO_SIGN, 0, 0, '{', '[', 0,
	0, 0, 0, 0, 0, '}', ']', 0,
	0, 0, 0, 0, 0, 0, '\\', 0,
	0, 0, 0, 0, 0, 0, 0, 0,
	0 /*CapsLock*/, 0 /*Rshift*/, PS2_ENTER /*Enter*/, '~', 0, '#', 0, 0,
	0, '|', 0, 0, 0, 0, PS2_BACKSPACE, 0,
	0, '1', 0, '4', '7', 0, 0, 0,
	'0', '.', '2', '5', '6', '8', PS2_ESC, 0 /*NumLock*/,
	PS2_F11, '+', '3', '-', '*', '9', PS2_SCROLL, 0,
	0, 0, 0, PS2_F7 },
  0,
};


const PS2Keymap_t PS2Keymap_French = {
  // without shift
	{0, PS2_F9, 0, PS2_F5, PS2_F3, PS2_F1, PS2_F2, PS2_F12,
	0, PS2_F10, PS2_F8, PS2_F6, PS2_F4, PS2_TAB, PS2_SUPERSCRIPT_TWO, 0,
	0, 0 /*Lalt*/, 0 /*Lshift*/, 0, 0 /*Lctrl*/, 'a', '&', 0,
	0, 0, 'w', 's', 'q', 'z', PS2_e_ACUTE, 0,
	0, 'c', 'x', 'd', 'e', '\'', '"', 0,
	0, ' ', 'v', 'f', 't', 'r', '(', 0,
	0, 'n', 'b', 'h', 'g', 'y', '-', 0,
	0, 0, ',', 'j', 'u', PS2_e_GRAVE, '_', 0,
	0, ';', 'k', 'i', 'o', PS2_a_GRAVE, PS2_c_CEDILLA, 0,
	0, ':', '!', 'l', 'm', 'p', ')', 0,
	0, 0, PS2_u_GRAVE, 0, '^', '=', 0, 0,
	0 /*CapsLock*/, 0 /*Rshift*/, PS2_ENTER /*Enter*/, '$', 0, '*', 0, 0,
	0, '<', 0, 0, 0, 0, PS2_BACKSPACE, 0,
	0, '1', 0, '4', '7', 0, 0, 0,
	'0', '.', '2', '5', '6', '8', PS2_ESC, 0 /*NumLock*/,
	PS2_F11, '+', '3', '-', '*', '9', PS2_SCROLL, 0,
	0, 0, 0, PS2_F7 },
  // with shift
	{0, PS2_F9, 0, PS2_F5, PS2_F3, PS2_F1, PS2_F2, PS2_F12,
	0, PS2_F10, PS2_F8, PS2_F6, PS2_F4, PS2_TAB, 0, 0,
	0, 0 /*Lalt*/, 0 /*Lshift*/, 0, 0 /*Lctrl*/, 'A', '1', 0,
	0, 0, 'W', 'S', 'Q', 'Z', '2', 0,
	0, 'C', 'X', 'D', 'E', '4', '3', 0,
	0, ' ', 'V', 'F', 'T', 'R', '5', 0,
	0, 'N', 'B', 'H', 'G', 'Y', '6', 0,
	0, 0, '?', 'J', 'U', '7', '8', 0,
	0, '.', 'K', 'I', 'O', '0', '9', 0,
	0, '/', PS2_SECTION_SIGN, 'L', 'M', 'P', PS2_DEGREE_SIGN, 0,
	0, 0, '%', 0, PS2_DIAERESIS, '+', 0, 0,
	0 /*CapsLock*/, 0 /*Rshift*/, PS2_ENTER /*Enter*/, PS2_POUND_SIGN, 0, PS2_MICRO_SIGN, 0, 0,
	0, '>', 0, 0, 0, 0, PS2_BACKSPACE, 0,
	0, '1', 0, '4', '7', 0, 0, 0,
	'0', '.', '2', '5', '6', '8', PS2_ESC, 0 /*NumLock*/,
	PS2_F11, '+', '3', '-', '*', '9', PS2_SCROLL, 0,
	0, 0, 0, PS2_F7 },
	1,
  // with altgr
	{0, PS2_F9, 0, PS2_F5, PS2_F3, PS2_F1, PS2_F2, PS2_F12,
	0, PS2_F10, PS2_F8, PS2_F6, PS2_F4, PS2_TAB, 0, 0,
	0, 0 /*Lalt*/, 0 /*Lshift*/, 0, 0 /*Lctrl*/, '@', 0, 0,
	0, 0, 0, 0, 0, 0, '~', 0,
	0, 0, 0, 0, 0 /*PS2_EURO_SIGN*/, '{', '#', 0,
	0, 0, 0, 0, 0, 0, '[', 0,
	0, 0, 0, 0, 0, 0, '|', 0,
	0, 0, 0, 0, 0, '`', '\\', 0,
	0, 0, 0, 0, 0, '@', '^', 0,
	0, 0, 0, 0, 0, 0, ']', 0,
	0, 0, 0, 0, 0, 0, '}', 0,
	0 /*CapsLock*/, 0 /*Rshift*/, PS2_ENTER /*Enter*/, PS2_CURRENCY_SIGN, 0, '#', 0, 0,
	0, '|', 0, 0, 0, 0, PS2_BACKSPACE, 0,
	0, '1', 0, '4', '7', 0, 0, 0,
	'0', '.', '2', '5', '6', '8', PS2_ESC, 0 /*NumLock*/,
	PS2_F11, '+', '3', '-', '*', '9', PS2_SCROLL, 0,
	0, 0, 0, PS2_F7 }
};

const PS2Keymap_t PS2Keymap_Spanish = {
		// without shift
		{0, PS2_F9, 0, PS2_F5, PS2_F3, PS2_F1, PS2_F2, PS2_F12,
		 0, PS2_F10, PS2_F8, PS2_F6, PS2_F4, PS2_TAB, PS2_MASCULINE_ORDINAL, 0,
		 0, 0 /*Lalt*/, 0 /*Lshift*/, 0, 0 /*Lctrl*/, 'q', '1', 0,
		 0, 0, 'z', 's', 'a', 'w', '2', 0,
		 0, 'c', 'x', 'd', 'e', '4', '3', 0,
		 0, ' ', 'v', 'f', 't', 'r', '5', 0,
		 0, 'n', 'b', 'h', 'g', 'y', '6', 0,
		 0, 0, 'm', 'j', 'u', '7', '8', 0,
		 0, ',', 'k', 'i', 'o', '0', '9', 0,
		 0, '.', '-', 'l', 'n', 'p', '\'', 0,
		 0, 0, PS2_ACUTE_ACCENT, 0, '`', PS2_INVERTED_EXCLAMATION, 0, 0,
		 0 /*CapsLock*/, 0 /*Rshift*/, PS2_ENTER /*Enter*/, '+', 0, PS2_c_CEDILLA, 0, 0,
		 0, '<', 0, 0, 0, 0, PS2_BACKSPACE, 0,
		 0, '1', 0, '4', '7', 0, 0, 0,
		 '0', '.', '2', '5', '6', '8', PS2_ESC, 0 /*NumLock*/,
		 PS2_F11, '+', '3', '-', '*', '9', PS2_SCROLL, 0,
		 0, 0, 0, PS2_F7 },
		// with shift
		{0, PS2_F9, 0, PS2_F5, PS2_F3, PS2_F1, PS2_F2, PS2_F12,
		 0, PS2_F10, PS2_F8, PS2_F6, PS2_F4, PS2_TAB, PS2_FEMININE_ORDINAL, 0,
		 0, 0 /*Lalt*/, 0 /*Lshift*/, 0, 0 /*Lctrl*/, 'Q', '!', 0,
		 0, 0, 'Z', 'S', 'A', 'W', '\"', 0,
		 0, 'C', 'X', 'D', 'E', '$', PS2_MIDDLE_DOT, 0,
		 0, ' ', 'V', 'F', 'T', 'R', '%', 0,
		 0, 'N', 'B', 'H', 'G', 'Y', '&', 0,
		 0, 0, 'M', 'J', 'U', '/', '(', 0,
		 0, ';', 'K', 'I', 'O', '=', ')', 0,
		 0, ':', '_', 'L', 'N', 'P', '?', 0,
		 0, 0, PS2_DIAERESIS, 0, '^', PS2_INVERTED_QUESTION_MARK, 0, 0,
		 0 /*CapsLock*/, 0 /*Rshift*/, PS2_ENTER /*Enter*/, '*', 0, PS2_C_CEDILLA, 0, 0,
		 0, '>', 0, 0, 0, 0, PS2_BACKSPACE, 0,
		 0, '1', 0, '4', '7', 0, 0, 0,
		 '0', '.', '2', '5', '6', '8', PS2_ESC, 0 /*NumLock*/,
		 PS2_F11, '+', '3', '-', '*', '9', PS2_SCROLL, 0,
		 0, 0, 0, PS2_F7 },
         1,
		// with altgr
		{0, PS2_F9, 0, PS2_F5, PS2_F3, PS2_F1, PS2_F2, PS2_F12,
		 0, PS2_F10, PS2_F8, PS2_F6, PS2_F4, PS2_TAB, '\\', 0,
		 0, 0 /*Lalt*/, 0 /*Lshift*/, 0, 0 /*Lctrl*/, 'q', '|', 0,
		 0, 0, 'z', 's', 'a', 'w', '@', 0,
		 0, 'c', 'x', 'd', PS2_EURO_SIGN, '~', '#', 0,
		 0, ' ', 'v', 'f', 't', 'r', '5', 0,
		 0, 'n', 'b', 'h', 'g', 'y', PS2_NOT_SIGN, 0,
		 0, 0, 'm', 'j', 'u', '7', '8', 0,
		 0, ',', 'k', 'i', 'o', '0', '9', 0,
		 0, '.', '-', 'l', 'n', 'p', '\'', 0,
		 0, 0, '{', 0, '[', PS2_INVERTED_EXCLAMATION, 0, 0,
		 0 /*CapsLock*/, 0 /*Rshift*/, PS2_ENTER /*Enter*/, ']', 0, '}', 0, 0,
		 0, '|', 0, 0, 0, 0, PS2_BACKSPACE, 0,
		 0, '1', 0, '4', '7', 0, 0, 0,
		 '0', '.', '2', '5', '6', '8', PS2_ESC, 0 /*NumLock*/,
		 PS2_F11, '+', '3', '-', '*', '9', PS2_SCROLL, 0,
		 0, 0, 0, PS2_F7 }
};

const PS2Keymap_t PS2Keymap_Italian = {
		// without shift
		{0, PS2_F9, 0, PS2_F5, PS2_F3, PS2_F1, PS2_F2, PS2_F12,
		 0, PS2_F10, PS2_F8, PS2_F6, PS2_F4, PS2_TAB, '\\', 0,
		 0, 0 /*Lalt*/, 0 /*Lshift*/, 0, 0 /*Lctrl*/, 'q', '1', 0,
		 0, 0, 'z', 's', 'a', 'w', '2', 0,
		 0, 'c', 'x', 'd', 'e', '4', '3', 0,
		 0, ' ', 'v', 'f', 't', 'r', '5', 0,
		 0, 'n', 'b', 'h', 'g', 'y', '6', 0,
		 0, 0, 'm', 'j', 'u', '7', '8', 0,
		 0, ',', 'k', 'i', 'o', '0', '9', 0,
		 0, '.', '-', 'l', PS2_o_GRAVE, 'p', '\'', 0,
		 0, 0, PS2_a_GRAVE, 0, PS2_e_GRAVE, PS2_i_GRAVE, 0, 0,
		 0 /*CapsLock*/, 0 /*Rshift*/, PS2_ENTER /*Enter*/, '+', 0, PS2_u_GRAVE, 0, 0,
		 0, '<', 0, 0, 0, 0, PS2_BACKSPACE, 0,
		 0, '1', 0, '4', '7', 0, 0, 0,
		 '0', '.', '2', '5', '6', '8', PS2_ESC, 0 /*NumLock*/,
		 PS2_F11, '+', '3', '-', '*', '9', PS2_SCROLL, 0,
		 0, 0, 0, PS2_F7 },
		// with shift
		{0, PS2_F9, 0, PS2_F5, PS2_F3, PS2_F1, PS2_F2, PS2_F12,
		 0, PS2_F10, PS2_F8, PS2_F6, PS2_F4, PS2_TAB, '|', 0,
		 0, 0 /*Lalt*/, 0 /*Lshift*/, 0, 0 /*Lctrl*/, 'Q', '!', 0,
		 0, 0, 'Z', 'S', 'A', 'W', '\"', 0,
		 0, 'C', 'X', 'D', 'E', '$', PS2_POUND_SIGN, 0,
		 0, ' ', 'V', 'F', 'T', 'R', '%', 0,
		 0, 'N', 'B', 'H', 'G', 'Y', '&', 0,
		 0, 0, 'M', 'J', 'U', '/', '(', 0,
		 0, ';', 'K', 'I', 'O', '=', ')', 0,
		 0, ':', '_', 'L', PS2_c_CEDILLA, 0, '?', 0,
		 0, 0, PS2_DEGREE_SIGN, 0, PS2_e_ACUTE, '^', 0, 0,
		 0 /*CapsLock*/, 0 /*Rshift*/, PS2_ENTER /*Enter*/, '*', 0, PS2_SECTION_SIGN, 0, 0,
		 0, '>', 0, 0, 0, 0, PS2_BACKSPACE, 0,
		 0, '1', 0, '4', '7', 0, 0, 0,
		 '0', '.', '2', '5', '6', '8', PS2_ESC, 0 /*NumLock*/,
		 PS2_F11, '+', '3', '-', '*', '9', PS2_SCROLL, 0,
		 0, 0, 0, PS2_F7 },
         1,
		// with altgr
		{0, PS2_F9, 0, PS2_F5, PS2_F3, PS2_F1, PS2_F2, PS2_F12,
		 0, PS2_F10, PS2_F8, PS2_F6, PS2_F4, PS2_TAB, PS2_NOT_SIGN, 0,
		 0, 0 /*Lalt*/, 0 /*Lshift*/, 0, 0 /*Lctrl*/, 'q', PS2_SUPERSCRIPT_ONE, 0,
		 0, 0, 'z', 's', 'a', 'w', PS2_SUPERSCRIPT_TWO, 0,
		 0, 'c', 'x', 'd', PS2_EURO_SIGN, PS2_FRACTION_ONE_QUARTER, PS2_SUPERSCRIPT_THREE, 0,
		 0, ' ', 'v', 'f', 't', 'r', PS2_FRACTION_ONE_HALF, 0,
		 0, 'n', 'b', 'h', 'g', 'y', PS2_NOT_SIGN, 0,
		 0, 0, 'm', 'j', 'u', '{', '[', 0,
		 0, ',', 'k', 'i', 'o', '}', ']', 0,
		 0, '.', '-', 'l', '@', 'p', '\'', 0,
		 0, 0, '#', 0, '[', '~', 0, 0,
		 0 /*CapsLock*/, 0 /*Rshift*/, PS2_ENTER /*Enter*/, ']', 0, 0, 0, 0,
		 0, PS2_LEFT_DOUBLE_ANGLE_QUOTE, 0, 0, 0, 0, PS2_BACKSPACE, 0,
		 0, '1', 0, '4', '7', 0, 0, 0,
		 '0', '.', '2', '5', '6', '8', PS2_ESC, 0 /*NumLock*/,
		 PS2_F11, '+', '3', '-', '*', '9', PS2_SCROLL, 0,
		 0, 0, 0, PS2_F7 }
};

const PS2Keymap_t PS2Keymap_UK = {
// https://github.com/PaulStoffregen/PS2Keyboard/issues/15
  // without shift
	{0, PS2_F9, 0, PS2_F5, PS2_F3, PS2_F1, PS2_F2, PS2_F12,
	0, PS2_F10, PS2_F8, PS2_F6, PS2_F4, PS2_TAB, '`', 0,
	0, 0 /*Lalt*/, 0 /*Lshift*/, 0, 0 /*Lctrl*/, 'q', '1', 0,
	0, 0, 'z', 's', 'a', 'w', '2', 0,
	0, 'c', 'x', 'd', 'e', '4', '3', 0,
	0, ' ', 'v', 'f', 't', 'r', '5', 0,
	0, 'n', 'b', 'h', 'g', 'y', '6', 0,
	0, 0, 'm', 'j', 'u', '7', '8', 0,
	0, ',', 'k', 'i', 'o', '0', '9', 0,
	0, '.', '/', 'l', ';', 'p', '-', 0,
	0, 0, '\'', 0, '[', '=', 0, 0,
	0 /*CapsLock*/, 0 /*Rshift*/, PS2_ENTER /*Enter*/, ']', 0, '#', 0, 0,
	0, '\\', 0, 0, 0, 0, PS2_BACKSPACE, 0,
	0, '1', 0, '4', '7', 0, 0, 0,
	'0', '.', '2', '5', '6', '8', PS2_ESC, 0 /*NumLock*/,
	PS2_F11, '+', '3', '-', '*', '9', PS2_SCROLL, 0,
	0, 0, 0, PS2_F7 },
  // with shift
	{0, PS2_F9, 0, PS2_F5, PS2_F3, PS2_F1, PS2_F2, PS2_F12,
	0, PS2_F10, PS2_F8, PS2_F6, PS2_F4, PS2_TAB, 172 /* ¬ */, 0,
	0, 0 /*Lalt*/, 0 /*Lshift*/, 0, 0 /*Lctrl*/, 'Q', '!', 0,
	0, 0, 'Z', 'S', 'A', 'W', '"', 0,
	0, 'C', 'X', 'D', 'E', '$', 163 /* £ */, 0,
	0, ' ', 'V', 'F', 'T', 'R', '%', 0,
	0, 'N', 'B', 'H', 'G', 'Y', '^', 0,
	0, 0, 'M', 'J', 'U', '&', '*', 0,
	0, '<', 'K', 'I', 'O', ')', '(', 0,
	0, '>', '?', 'L', ':', 'P', '_', 0,
	0, 0, '@', 0, '{', '+', 0, 0,
	0 /*CapsLock*/, 0 /*Rshift*/, PS2_ENTER /*Enter*/, '}', 0, '~', 0, 0,
	0, '|', 0, 0, 0, 0, PS2_BACKSPACE, 0,
	0, '1', 0, '4', '7', 0, 0, 0,
	'0', '.', '2', '5', '6', '8', PS2_ESC, 0 /*NumLock*/,
	PS2_F11, '+', '3', '-', '*', '9', PS2_SCROLL, 0,
	0, 0, 0, PS2_F7 },
	0
};
#endif
#endif
